cidermole/yaca/eagle/phmeter.gif

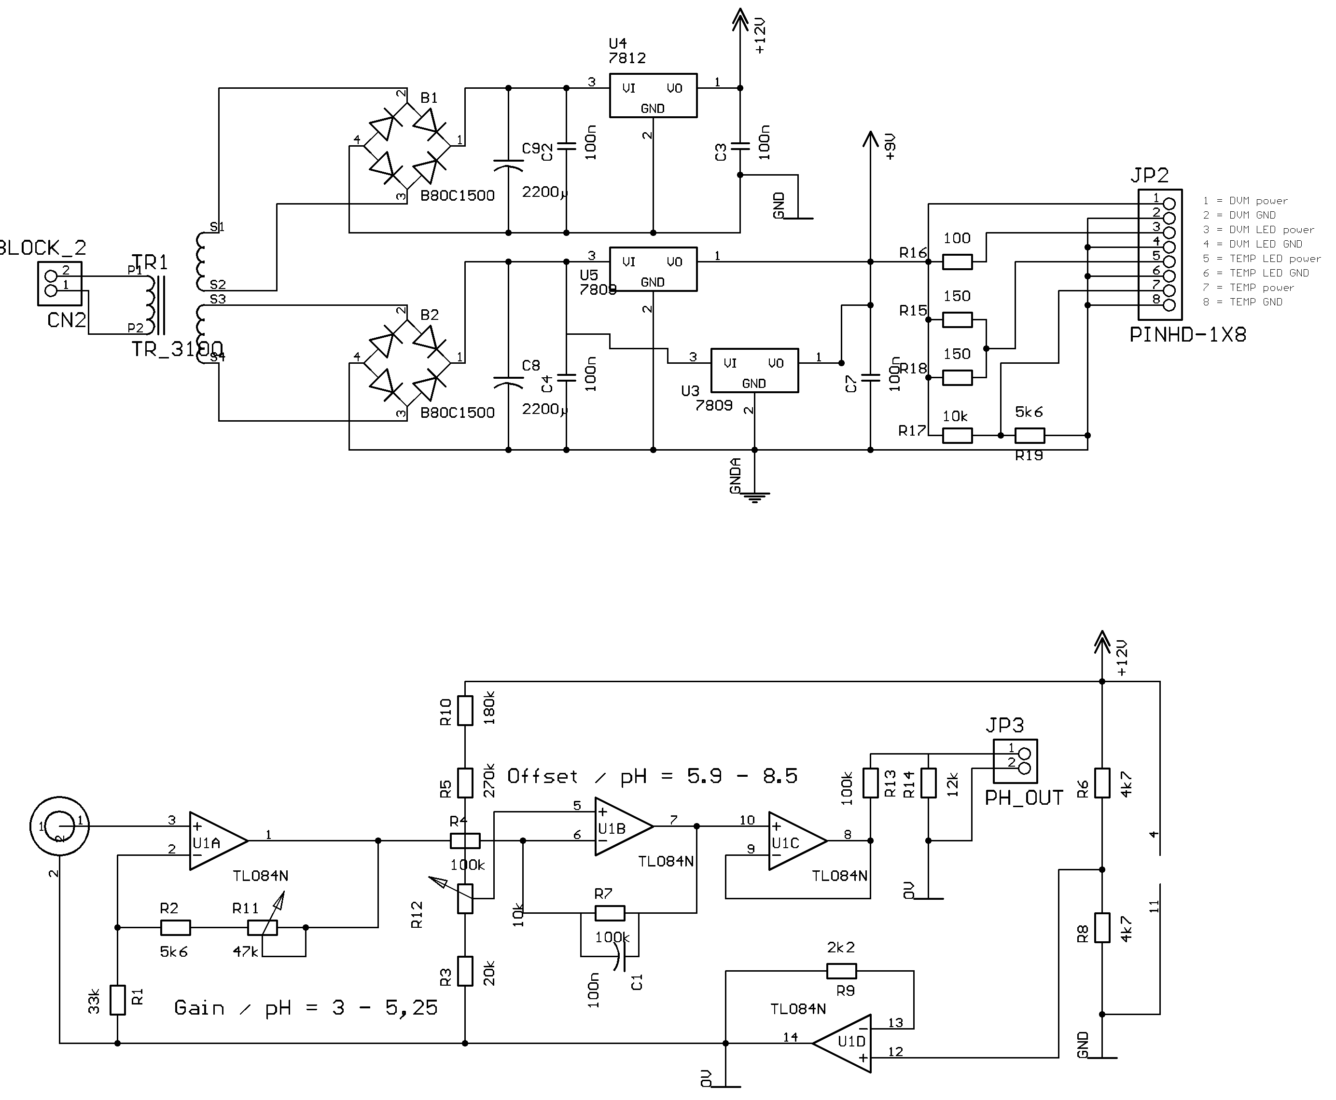
eagle/phmeter.gif
