cidermole/yaca/geda/switching-sim/switcher_new_diodes2.asc

C1: cap; 1µ; Rser=0.001 Lser=10n
C2: cap; 1000µ; Rser=0.03
C3: cap; 1000µ; Rser=0.03
C4: cap; 100n; Rser=0.001 Lser=10n
D3: diode; 1N4148
E1: e; 1
E2: e; 1
E3: e; 1000
E4: e; 10
E5: e; 1
E6: e; 1
L1: ind2; 20µ; Rser=0.1
L2: ind2; 20µ; Rser=0.1
L3: ind2; 11.2µ; Rser=0.01
L4: ind2; 11.2µ; Rser=0.01
M1: nmos; IRFP90N20D
M2: nmos; IRFP90N20D
M3: nmos; FDS5680
M4: nmos; FDS5680
R1: res; 8
R2: res; 8
R3: res; 4.76
R4: res; 4k
R5: res; 16k
R6: res; 1k
R7: res; 1k
R8: res; 0.001
R9: res; 100k
R10: res; 1k
R11: res; 100
R12: res; 8
R13: res; 8
U1: LT1011
U2: LT1011
V1: voltage; 20; Rser=0.3
V2: voltage; PULSE(-1 10 1µ 10µ 20n 20n 20µ)
V3: voltage; PULSE(-1 10 11µ 10µ 20n 20n 20µ)
V4: voltage; 10
Named nets: Vres1, Vres2, 0, Ushunt, Umag, G1, G2, Vout
K1 L1 L2 L3 L4 1
.tran 5m startup
