cidermole/yaca/geda/switching-sim/etc/Draft1.asc

C1: cap; 1µ
D1: zener; BZX84C15L
D2: zener; BZX84C15L
D3: diode; 1N4148
D4: diode; 1N4148
L1: ind2; 20µ
L2: ind2; 20µ
L3: ind2; 20µ
L4: ind; 200µ; Rser=0.02
M1: nmos; IRFP90N20D
M2: nmos; IRFP90N20D
R1: res; 500
R2: res; 500
R3: res; 100
V1: voltage; 20; Rser=0.1
Named nets: 0, Vout, Vres1, Vres2
K1 L1 L2 L3 0.999
.tran 0.1
