cidermole/yaca/geda/switching-sim/etc/flyback.asc

C1: cap; 1000µ
C2: cap; 1000µ
L1: ind2; 100µ; Rser=0
L2: ind2; 100µ
M1: nmos; FDS5680
M2: nmos; FDS5680
R1: res; 10
V1: voltage; 20; Rser=0.03
V2: voltage; PULSE(0 10 0 20n 20n 5µ 10µ)
V3: voltage; PULSE(0 10 5µ 20n 20n 5µ 10µ)
Named nets: 0, Vout, Gate, ud
K1 L1 L2 1
.tran 30m startup
