cidermole/yaca/geda/switching-sim/etc/synchron.asc

L1: ind2; 10µ; Rser=0.001
L2: ind2; 10µ
M1: nmos; FDS5680
R1: res; 10
R2: res; 3
V1: voltage; SINE(0 10 100k)
V2: voltage; PULSE(0 10 0 20n 20n 5µ 10µ)
Named nets: 0, Uin, Vrect, Gate
K L1 L2 1
.tran 1m startup
