cidermole/yaca/src/embedded/control-panel/ControlPanel.h

#include "Messages.h"
#include <inttypes.h>

#define YC_EE_TCP_IN_ID YE(508) // int32
#define YC_EE_TCP_OUT_ID YE(504) // int32
#define YC_EE_TEMPSTATUS_ID YE(500) // int32
#define YC_EE_UBRR YE(498) // int16
#define YC_EE_TEMP_INTERVAL YE(496) // int16

namespace ControlPanel {
}
