cidermole/yaca/src/x86/mpmon/main.cpp

#include <stdio.h>
#include <stdint.h>
#include <stdlib.h>
#include <string.h>
#include <unistd.h>

#include "config.h"
#include "network.h"
#include "../yaca-path.h"

double uin_convert(int adc) {
	return ((double) adc) * 110.08 / 10240;
}

double iin_convert(int adc) {
	return ((double) adc) * 30.72 / 6545.408;
}

int main(int argc, char **argv) {
	int sock = 0;
	char config_file[1024];
	Message msg;
	
	init_yaca_path();
	sprintf(config_file, "%s/src/x86/mpmon/conf/mpmon.conf", yaca_path);
	load_conf(config_file);
	if((sock = connect_socket(conf.server, conf.port)) == -1)
		return 1;
	
	while(1) {
		if(!read_message(sock, &msg)) {
			printf("read_message() returned an error, sleeping 1 s...\n");
			usleep(1000 * 1000);
			continue;
		}
		if(msg.id != conf.status_canid || msg.rtr)
			continue;
		
		printf("AC status: %d  U_in: %03X (%02.2lf V)  I_in: %03X (%1.3lf)\n", msg.data[0], msg.data[1] * 0x100 + msg.data[2], uin_convert(msg.data[1] * 0x100 + msg.data[2]), msg.data[3] * 0x100 + msg.data[4], iin_convert(msg.data[3] * 0x100 + msg.data[4]));
	}

#ifdef _WIN32
	closesocket(sock);
#else
	close(sock);
#endif

	return 0;
}
