cidermole/yaca/src/embedded/radio-base/sender/rf12.h

extern unsigned short rf12_trans(unsigned short wert);					// transfer 1 word to/from module
extern void rf12_init(void);											// initialize module
extern void rf12_setfreq(unsigned short freq);							// set center frequency
extern void rf12_setbaud(unsigned short baud);							// set baudrate
extern void rf12_setpower(unsigned char power, unsigned char mod);		// set transmission settings
extern void rf12_setbandwidth(unsigned char bandwidth, unsigned char gain, unsigned char drssi);	// set receiver settings
extern void rf12_txdata(unsigned char *data, unsigned char number);		// transmit number of bytes from array
//extern void rf12_rxdata(unsigned char *data, unsigned char number);		// receive number of bytes into array
extern void rf12_ready(void);											// wait until FIFO ready (to transmit/read data)

extern void rf12_off(void);												// switch off crystal oscillator: < 1 uA
extern void rf12_on(void);												// switch on crystal oscillator
extern void rf12_timer(unsigned char mantissa, unsigned char exponent);	// enable sleep timer for (mantissa * 2^exponent) ms, switch off crystal
extern void rf12_timer(unsigned char mantissa, unsigned char exponent);	// enable sleep timer for (mantissa * 2^exponent) ms, switch off crystal

#define RF12FREQ(freq)	((freq-430.0)/0.0025)							// macro for calculating frequency value out of frequency in MHz
