cidermole/yaca/src/embedded/radio-base/librfm12/rfm12.h

#ifndef RFM12_H
#define RFM12_H

#ifdef __cplusplus
extern "C" {
#endif

#include "rfm12_stack.h"
#include "rfm12_llc.h"
#include "rfm12_phy.h"
#include "rfm12_mac.h"

#ifdef __cplusplus
}
#endif

#endif /* RFM12_H */
