cidermole/yaca/src/embedded/radio-base/librfm12/hamming.c

#include "hamming.h"

const prog_uint8_t _Hamming_enc[16] = {0x15,0x02,0x49,0x5E,0x64,0x73,0x38,0x2F,0xD0,0xC7,0x8C,0x9B,0xA1,0xB6,0xFD,0xEA};
const prog_uint8_t _Hamming_dec[256] = {
	0x01,0x00,0x01,0x01,0x00,0x00,0x01,0x01,0x02,0x02,0x01,0x03,0x0A,0x02,0x03,0x07,
	0x00,0x00,0x01,0x01,0x00,0x00,0x01,0x00,0x06,0x02,0x03,0x0B,0x02,0x00,0x03,0x03,
	0x04,0x0C,0x01,0x05,0x04,0x04,0x05,0x07,0x06,0x06,0x07,0x07,0x06,0x07,0x07,0x07,
	0x06,0x04,0x05,0x05,0x04,0x00,0x0D,0x05,0x06,0x06,0x06,0x07,0x06,0x06,0x07,0x07,
	0x00,0x02,0x01,0x01,0x04,0x00,0x01,0x09,0x02,0x02,0x03,0x02,0x02,0x02,0x03,0x03,
	0x08,0x00,0x01,0x05,0x00,0x00,0x03,0x01,0x02,0x02,0x03,0x03,0x03,0x02,0x03,0x03,
	0x04,0x04,0x05,0x05,0x04,0x04,0x04,0x05,0x06,0x02,0x0F,0x07,0x04,0x06,0x07,0x07,
	0x04,0x05,0x05,0x05,0x04,0x04,0x05,0x05,0x06,0x06,0x07,0x05,0x06,0x0E,0x03,0x07,
	0x08,0x0C,0x01,0x09,0x0A,0x08,0x09,0x09,0x0A,0x0A,0x0B,0x0B,0x0A,0x0A,0x0A,0x0B,
	0x08,0x08,0x09,0x0B,0x08,0x00,0x0D,0x09,0x0A,0x0B,0x0B,0x0B,0x0A,0x0A,0x0B,0x0B,
	0x0C,0x0C,0x0D,0x0C,0x0C,0x0C,0x0D,0x0D,0x0E,0x0C,0x0F,0x0F,0x0A,0x0E,0x0F,0x07,
	0x0C,0x0C,0x0D,0x0D,0x0D,0x0C,0x0D,0x0D,0x06,0x0E,0x0F,0x0B,0x0E,0x0E,0x0D,0x0F,
	0x08,0x08,0x09,0x09,0x08,0x09,0x09,0x09,0x0A,0x02,0x0F,0x0B,0x0A,0x0A,0x0B,0x09,
	0x08,0x08,0x08,0x09,0x08,0x08,0x09,0x09,0x08,0x0A,0x0B,0x0B,0x0A,0x0E,0x03,0x0B,
	0x0C,0x0C,0x0F,0x0D,0x04,0x0C,0x0D,0x09,0x0F,0x0E,0x0F,0x0F,0x0E,0x0E,0x0F,0x0F,
	0x08,0x0C,0x0D,0x05,0x0C,0x0E,0x0D,0x0D,0x0E,0x0E,0x0F,0x0F,0x0E,0x0E,0x0F,0x0E
};
