cidermole/yaca/src/x86/yaca-cached/network.h

#ifndef NETWORK_H
#define NETWORK_H

#include <stdint.h>

struct Message {
        uint8_t info;
        uint32_t id;
        uint8_t rtr;
        uint8_t length;
        uint8_t data[8];
} __attribute__((__packed__));


#define RTR_TIMEOUT_SEC 1
#define RTR_TIMEOUT_US  0


int connect_socket(const char *host, int port);

void write_message(int sock, unsigned int id, int length = 0, char d0 = 0, char d1 = 0, char d2 = 0, char d3 = 0, char d4 = 0, char d5 = 0, char d6 = 0, char d7 = 0);

int read_message(int sock, struct Message *buffer);

char *target_flash_page(const char *buffer, int page_size, int tid, int sock);

uint16_t crc16_update(uint16_t crc, uint8_t c);

void target_eeprom_write(uint32_t id, int sock, uint16_t addr, uint8_t data);

int create_host(int port);

#endif /* NETWORK_H */
